BreakfastStanford/StrumTechCapstoneProjectCopy/StrumTechCapstone/Senior_Design_Capstone_StrumTech-main/Senior_Design_Capstone_StrumTech-main/Esp32_bluetooth_test-3/Esp32_bluetooth_test-3/ControlData.ino

#include "ControlData.hpp"
  // sets mode data for next run
  void SetModeData()
  {
    CURRENT_MODE_SETTINGS = NEXT_MODE_SETTINGS;
  }

  enum ControlModes MapToMode(int mode)
  {
    if (mode == FREE_MODE_SETTIING)
    {
      return FREE_MODE_SETTIING;
    }
    else if (mode == TUNER_MODE_SETTING)
    {
      return TUNER_MODE_SETTING;
    } 
    else if (mode == CHORDS_MODE_SETTING)
    {
      return CHORDS_MODE_SETTING;
    }
    else 
    {
      return NO_MODE;
    }

  }
